second-string/spot-check-hardware/rev_2/Esp32Breakout1c _ ESP32.pdf

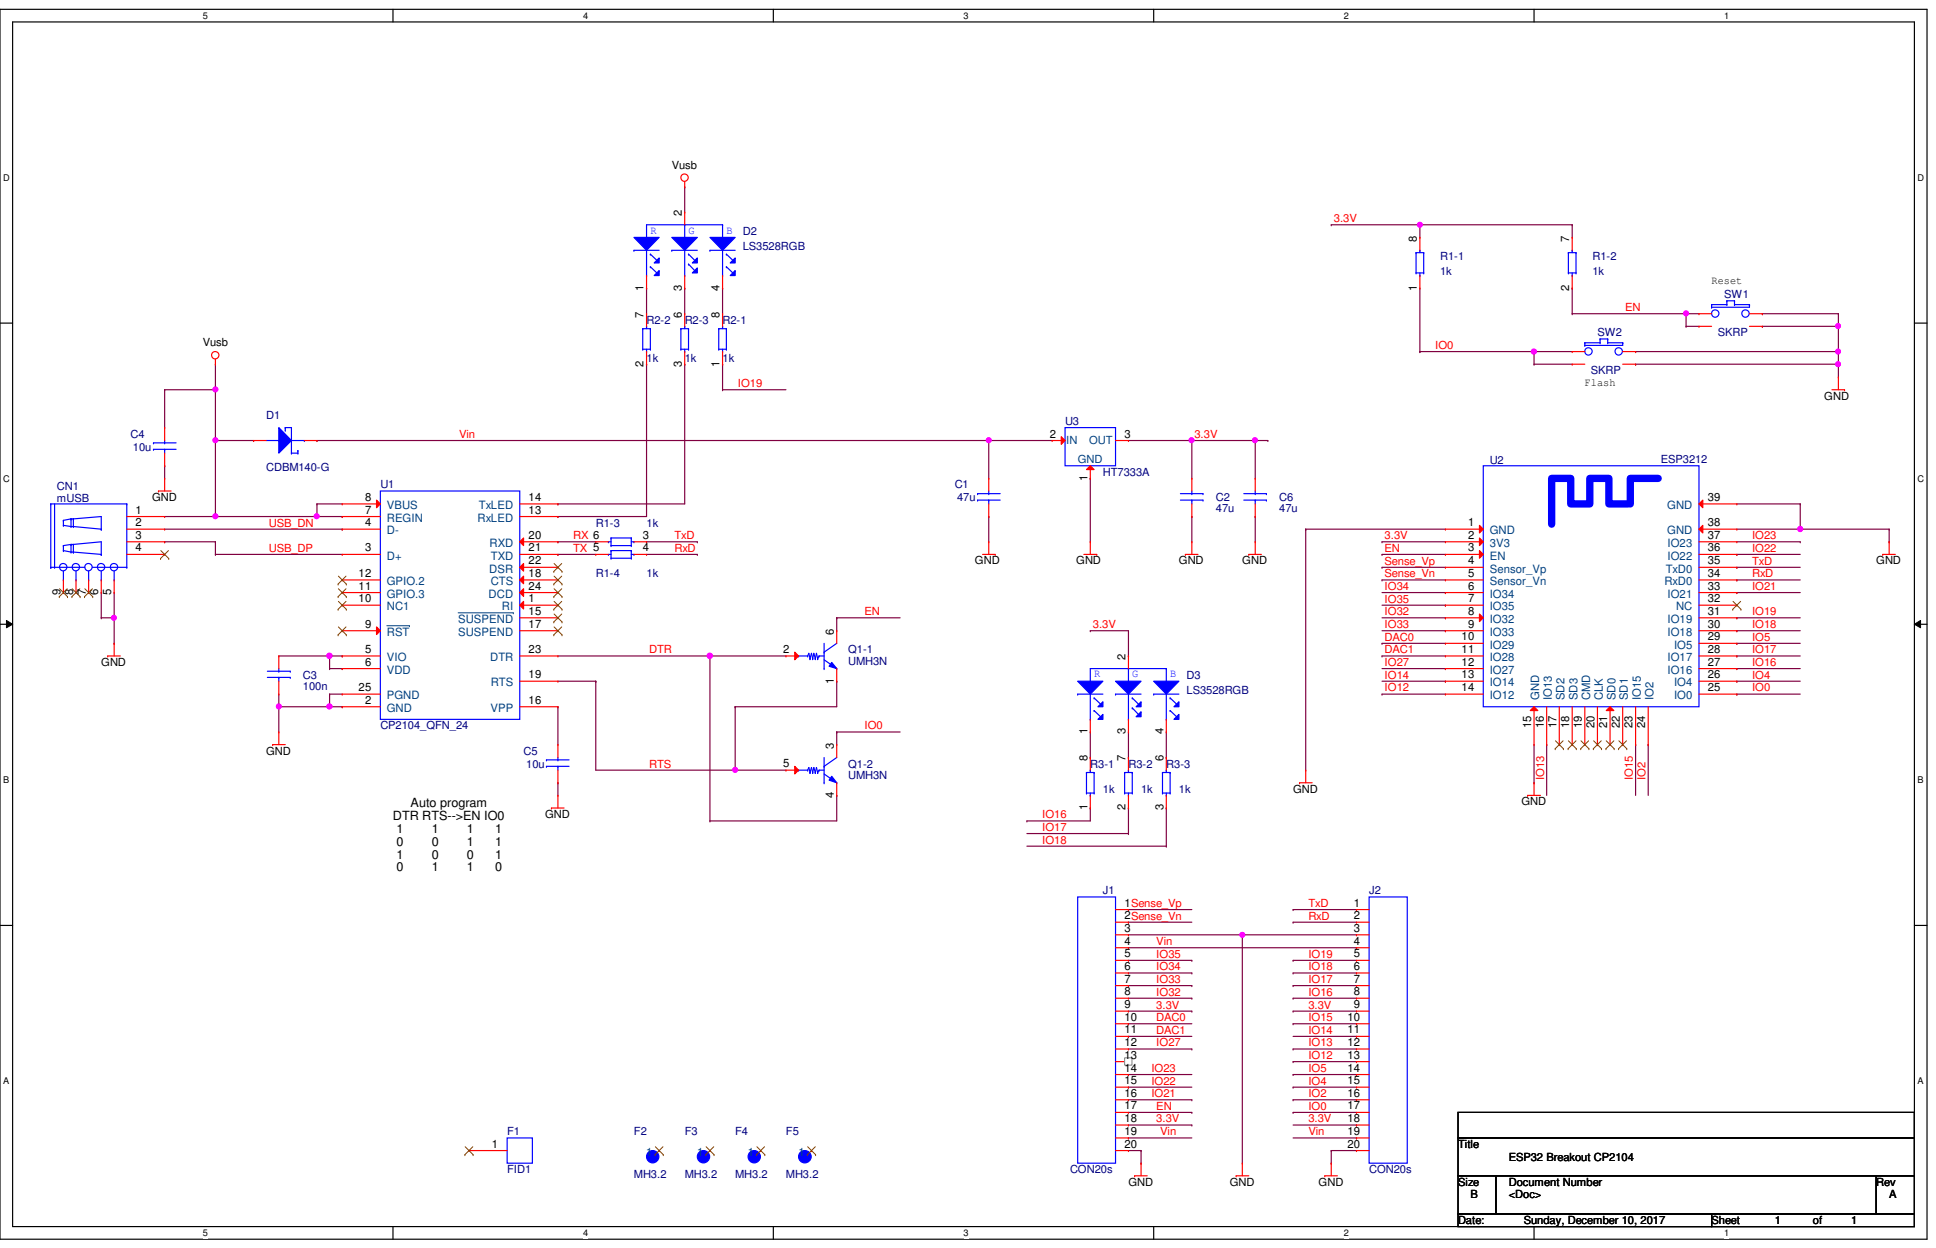
[picture p14: page 1]
