second-string/spot-check-hardware/rev_3/spot_check_rev_3_cream.pdf

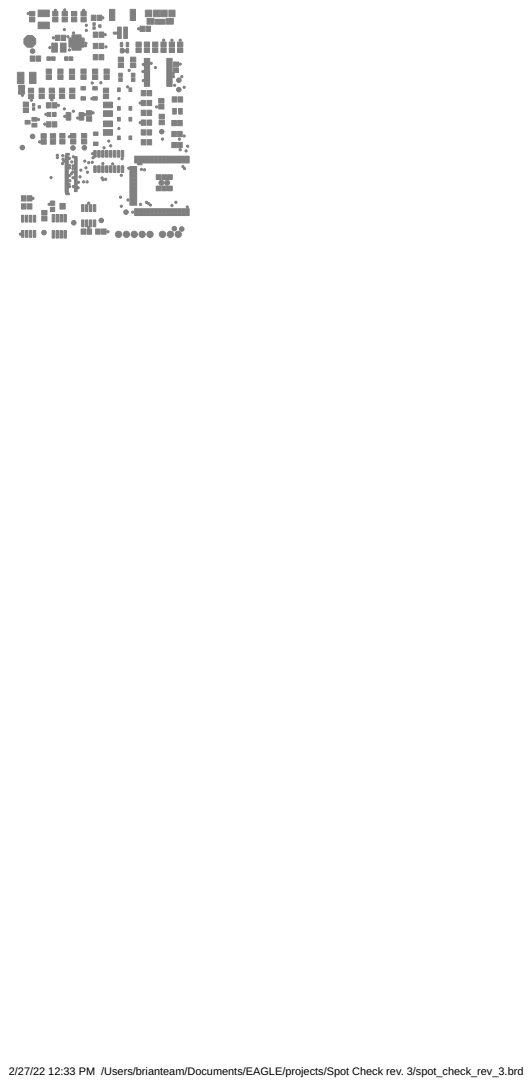
[picture p15: page 1]

2/27/22 12:33 PM /Users/brianteam/Documents/EAGLE/projects/Spot Check rev. 3/spot_check_rev_3.brd
